kikiisdead/minichord/src/userInterface/animation.h

#ifndef animation_h
#define animation_h

#include "interfaces/encoderEditable.h"

class Animation : public EncoderEditable {
public:
  Animation() {
    num = 4;
  }
  void increment() {}
  void decrement() {}
};

#endif
